AkshathRaghav/boilernet/model_train/models/cats_mobilenet_v2_accuracy.png

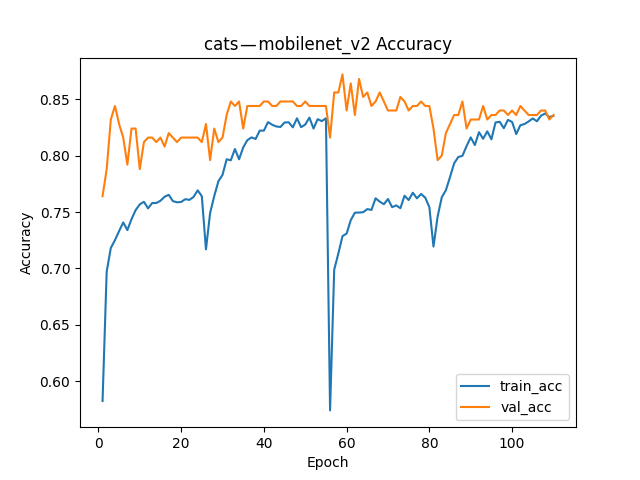
model_train/models/cats_mobilenet_v2_accuracy.png
