AkshathRaghav/boilernet/model_train/models/cats_mobilenet_v2_loss.png

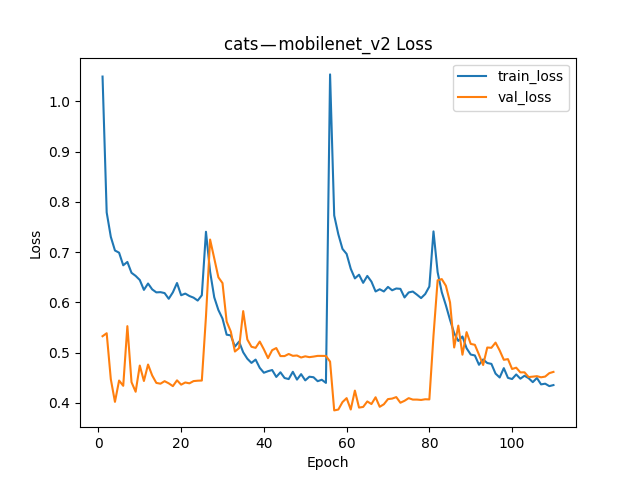
model_train/models/cats_mobilenet_v2_loss.png
