AkshathRaghav/boilernet/model_train/models/dogs_mobilenet_v2_accuracy.png

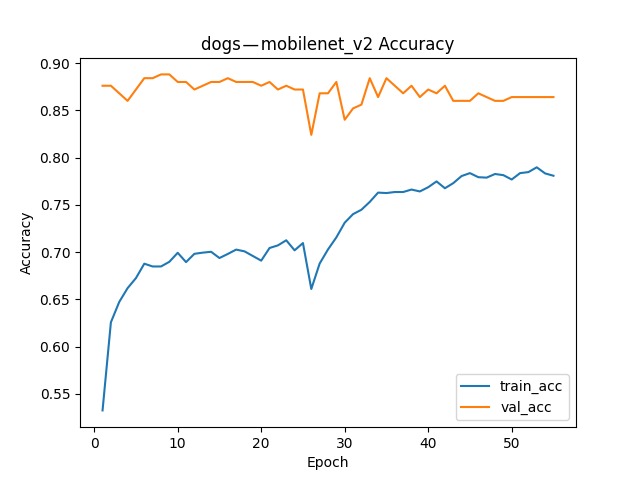
model_train/models/dogs_mobilenet_v2_accuracy.png
