AkshathRaghav/boilernet/model_train/models/dogs_mobilenet_v2_loss.png

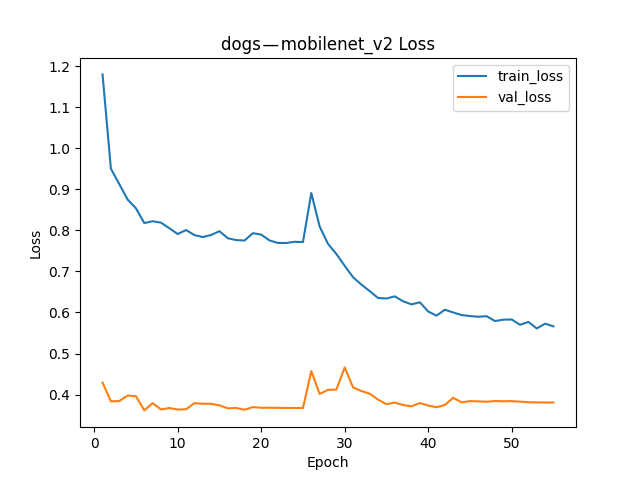
model_train/models/dogs_mobilenet_v2_loss.png
