AkshathRaghav/boilernet/model_train/models/fruits_mobilenet_v2_accuracy.png

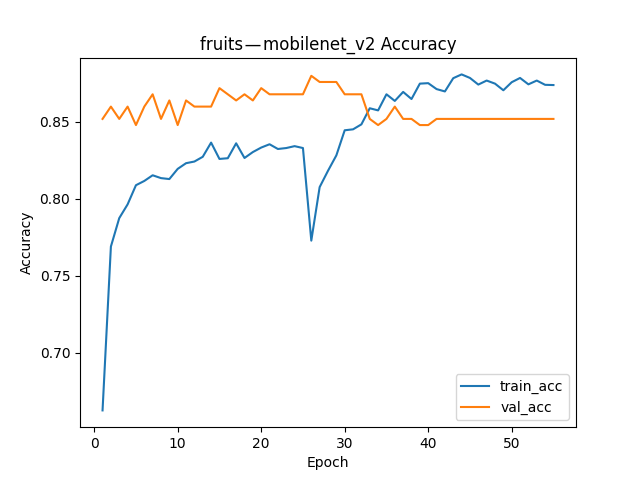
model_train/models/fruits_mobilenet_v2_accuracy.png
