AkshathRaghav/boilernet/model_train/models/fruits_mobilenet_v2_loss.png

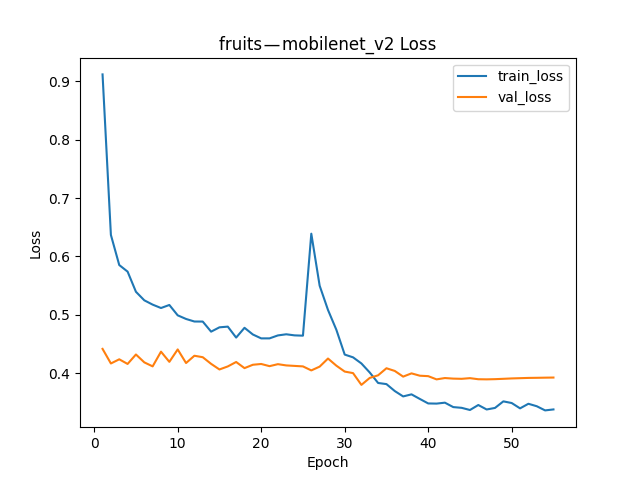
model_train/models/fruits_mobilenet_v2_loss.png
