AkshathRaghav/boilernet/model_train/models/kitchen_mobilenet_v2_accuracy.png

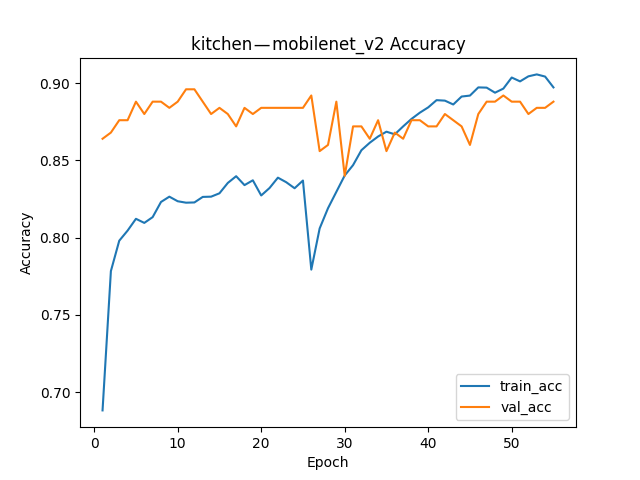
model_train/models/kitchen_mobilenet_v2_accuracy.png
