AkshathRaghav/boilernet/model_train/models/kitchen_mobilenet_v2_loss.png

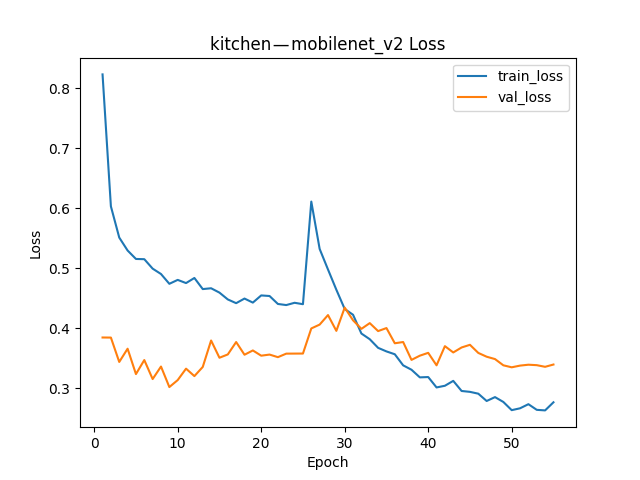
model_train/models/kitchen_mobilenet_v2_loss.png
