AkshathRaghav/boilernet/model_train/models/stationary_mobilenet_v2_accuracy.png

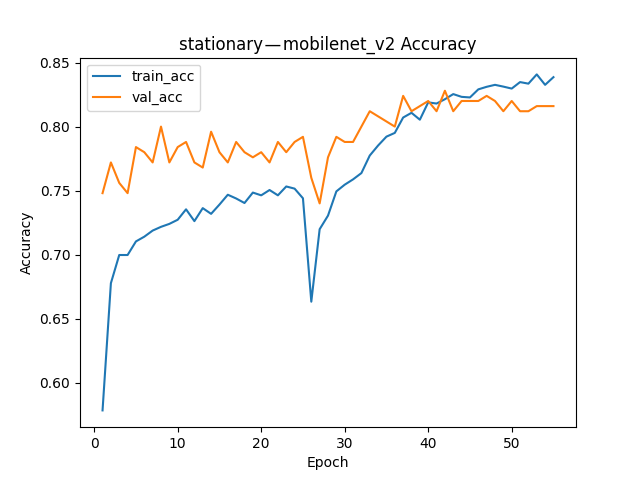
model_train/models/stationary_mobilenet_v2_accuracy.png
