AkshathRaghav/boilernet/model_train/models/stationary_mobilenet_v2_loss.png

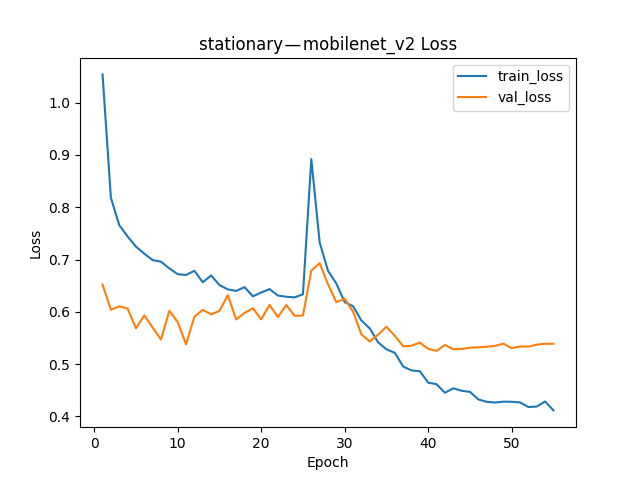
model_train/models/stationary_mobilenet_v2_loss.png
