AkshathRaghav/boilernet/src/compute_nodes/main/file01.jpg

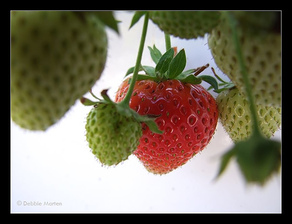
src/compute_nodes/main/file01.jpg
