AkshathRaghav/boilernet/src/fastapi_backend/input/file03.png

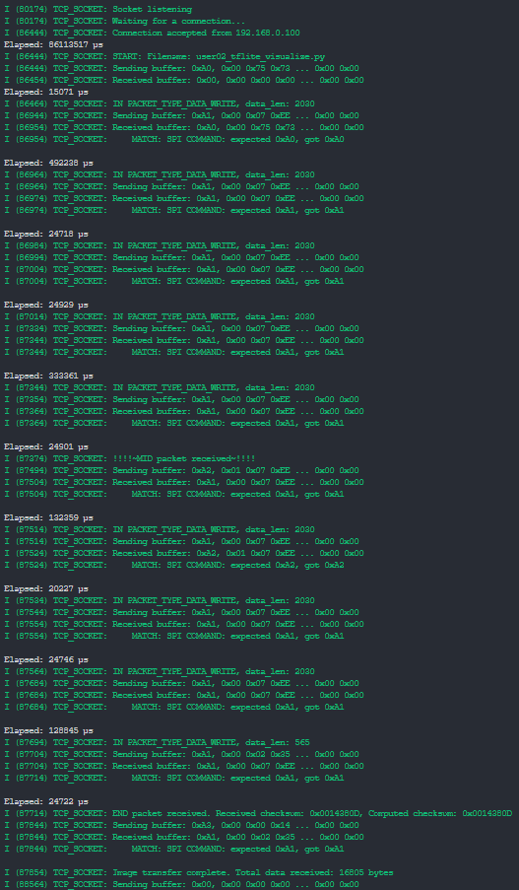
src/fastapi_backend/input/file03.png
