AkshathRaghav/boilernet/src/fastapi_backend/tmp/BoilerNet.png

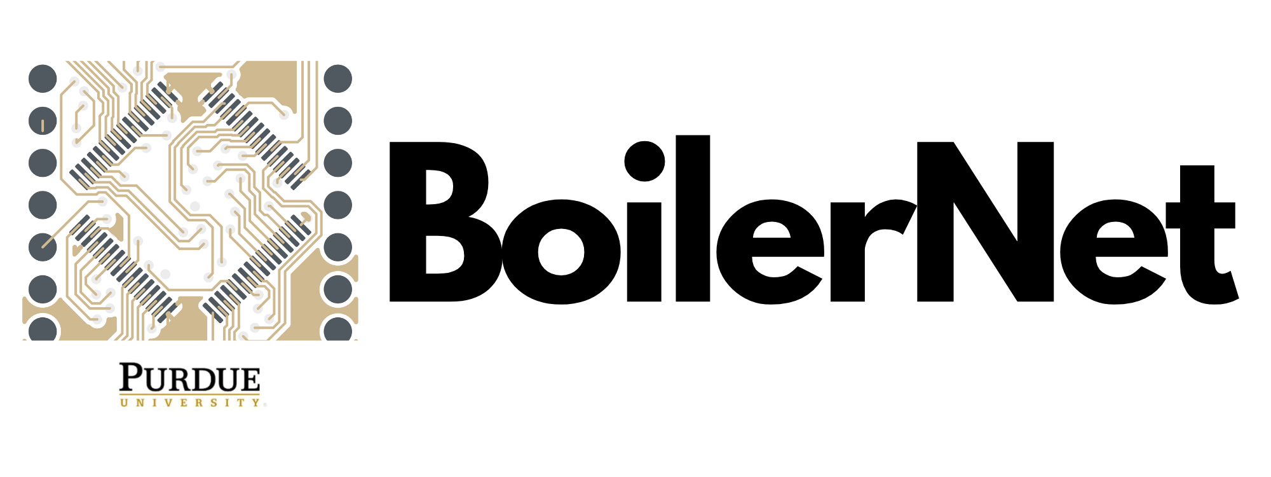
src/fastapi_backend/tmp/BoilerNet.png
