AkshathRaghav/boilernet/src/fastapi_backend/tmp/failed.png

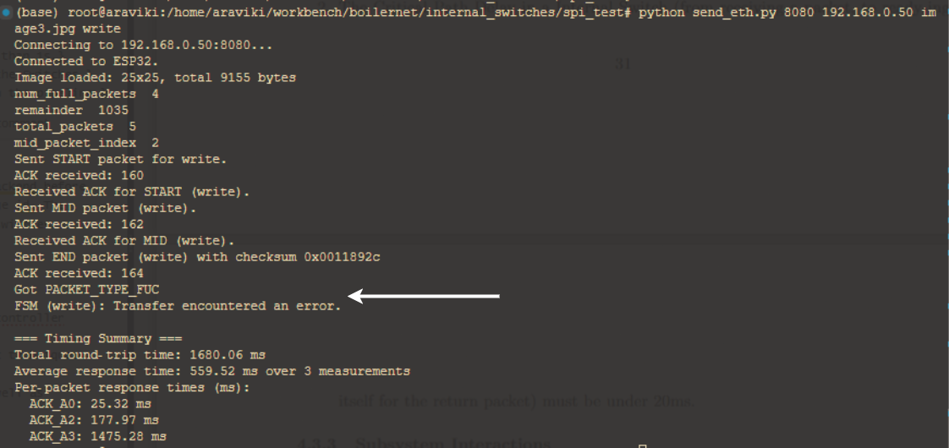
src/fastapi_backend/tmp/failed.png
