AkshathRaghav/boilernet/src/fastapi_backend/tmp/imageedit_9_5180436000.jpg

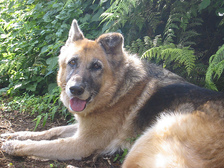
src/fastapi_backend/tmp/imageedit_9_5180436000.jpg
