AkshathRaghav/boilernet/src/fastapi_backend/tmp/imageedit_11_3820304279.jpg

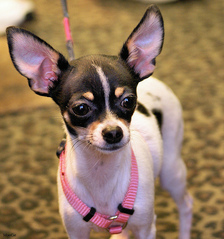
src/fastapi_backend/tmp/imageedit_11_3820304279.jpg
