AkshathRaghav/boilernet/src/fastapi_backend/tmp/send_file.png

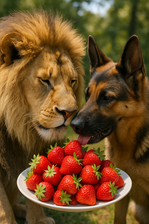
src/fastapi_backend/tmp/send_file.png
